BJRitchie/MTRX2700_A3/Joystick CAD Model/Joystick.SLDASM

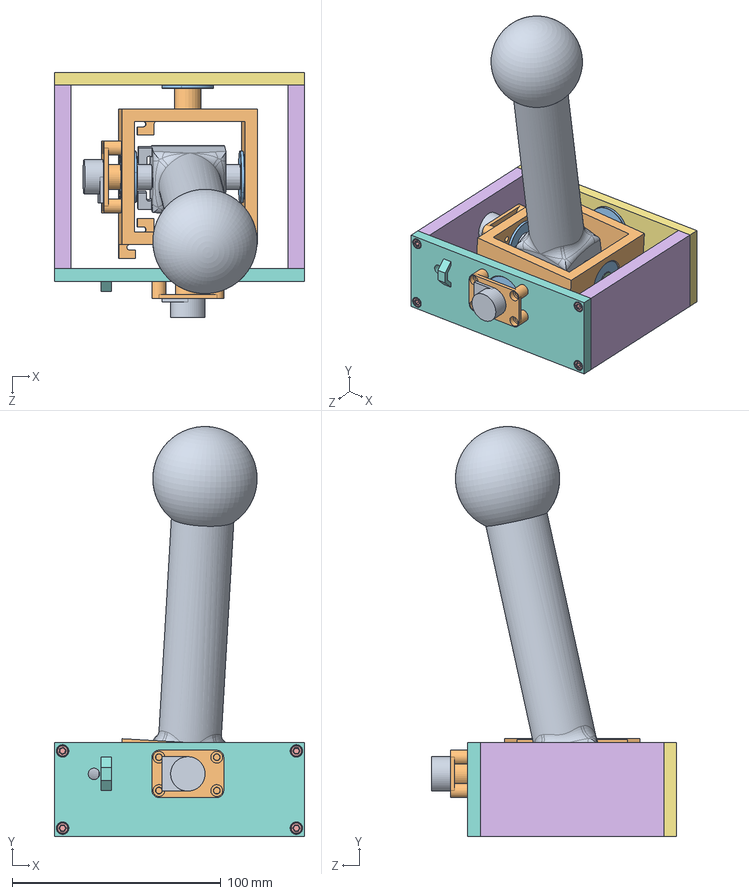
[picture p5: CAD file, 2024-05-18]
Joystick CAD Model/Joystick.SLDASM
120.0 x 196.4 x 117.4 mm
Inner Base
Handle
Main Base Bearing Side
Main Base Bearing Side Other
Main Base Side x 2
Socket Head M3x20 x 8
Axle
Bearing x 4
Potentiometer Standoff x 2
Potentiometer x 2
