BJRitchie/MTRX2700_A3/gimbal_design/x_rotation.SLDPRT

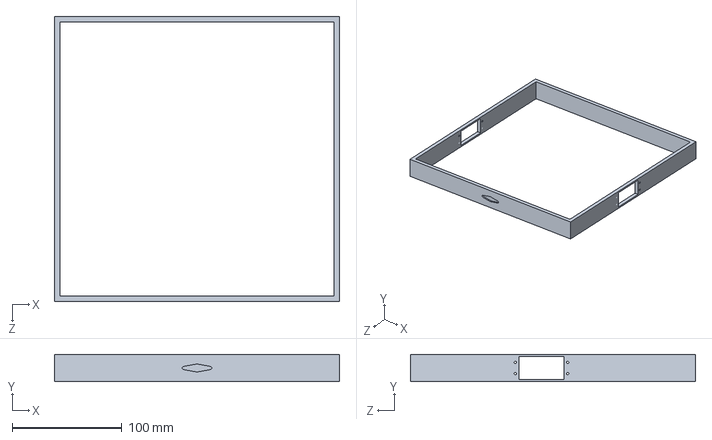
[picture p16: CAD file, 2024-05-07]
gimbal_design/x_rotation.SLDPRT
260.2 x 25.0 x 260.2 mm
