BJRitchie/MTRX2700_A3/gimbal_design/mock_horn.SLDPRT

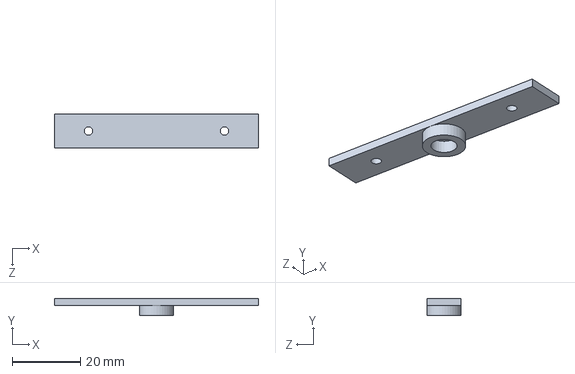
[picture p17: CAD file, 2024-05-07]
gimbal_design/mock_horn.SLDPRT
60.0 x 5.00 x 10.1 mm
