BJRitchie/MTRX2700_A3/Joystick CAD Model/Socket Head M3x20.SLDPRT

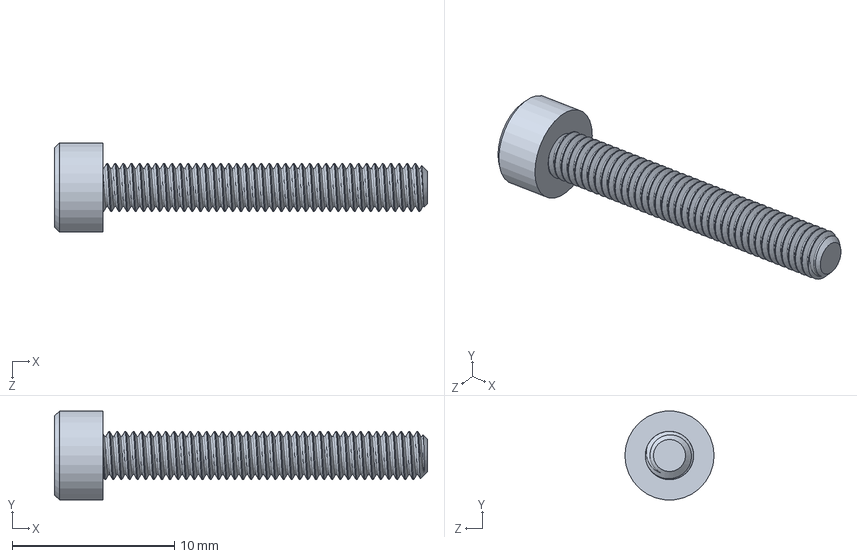
[picture p18: CAD file, 2024-05-18]
Joystick CAD Model/Socket Head M3x20.SLDPRT
23.0 x 5.47 x 5.50 mm
