BJRitchie/MTRX2700_A3/gimbal_design/HS-322HD-1642818504.stp

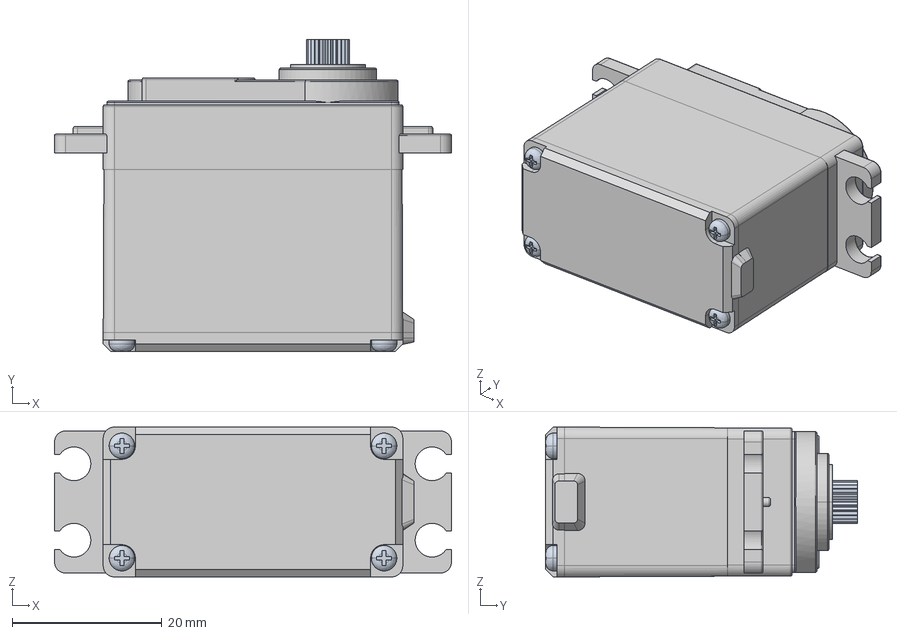
[picture p19: CAD file, 2024-05-04]
gimbal_design/HS-322HD-1642818504.stp
53.0 x 41.6 x 20.0 mm
