BJRitchie/MTRX2700_A3/Joystick CAD Model/Potentiometer Standoff.SLDPRT

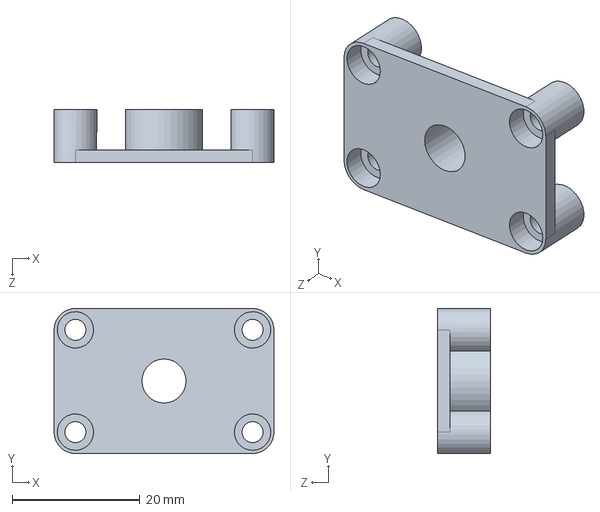
[picture p20: CAD file, 2024-05-18]
Joystick CAD Model/Potentiometer Standoff.SLDPRT
34.4 x 22.7 x 8.35 mm
