BJRitchie/MTRX2700_A3/Joystick CAD Model/Potentiometer.SLDPRT

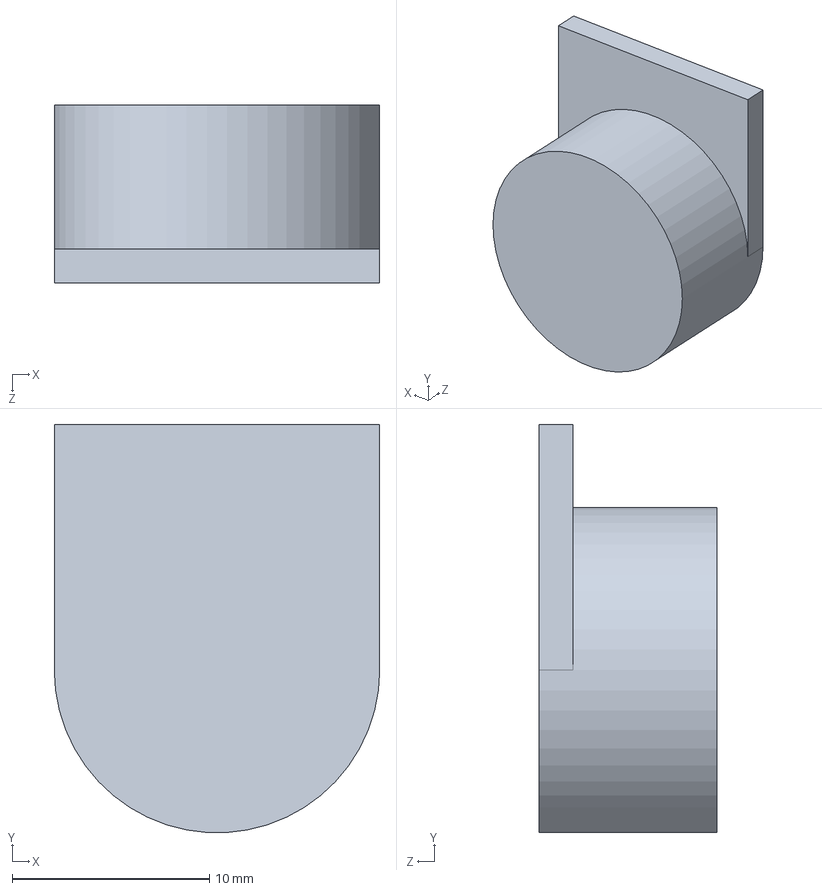
[picture p21: CAD file, 2024-05-18]
Joystick CAD Model/Potentiometer.SLDPRT
16.5 x 20.7 x 9.00 mm
