BJRitchie/MTRX2700_A3/Joystick CAD Model/Bearing.SLDPRT

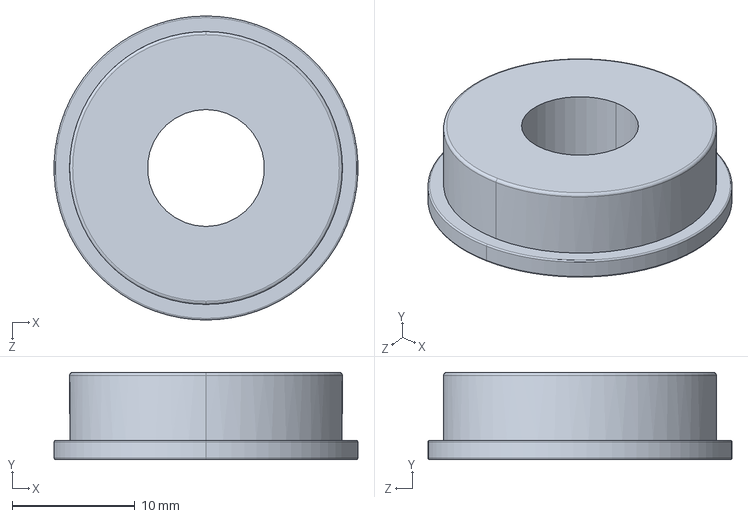
[picture p22: CAD file, 2024-05-18]
Joystick CAD Model/Bearing.SLDPRT
24.7 x 7.11 x 24.8 mm
