BJRitchie/MTRX2700_A3/Joystick CAD Model/Handle Quick Print 2.SLDPRT

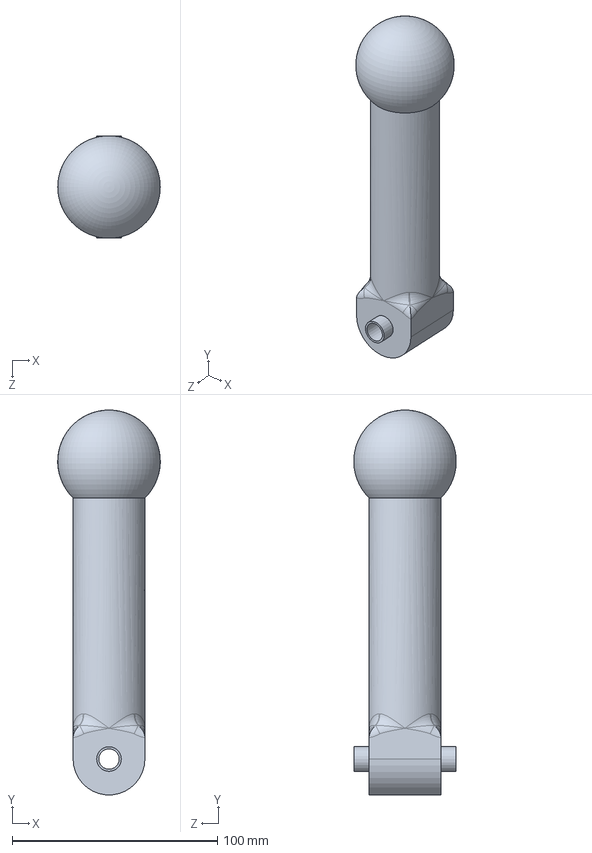
[picture p23: CAD file, 2024-05-18]
Joystick CAD Model/Handle Quick Print 2.SLDPRT
50.0 x 187.5 x 49.9 mm
