BJRitchie/MTRX2700_A3/Joystick CAD Model/Inner Base.SLDPRT

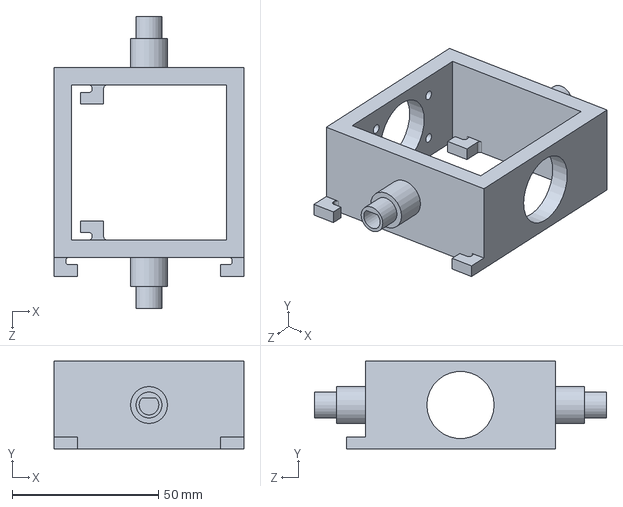
[picture p24: CAD file, 2024-05-18]
Joystick CAD Model/Inner Base.SLDPRT
65.0 x 30.0 x 100.0 mm
